4pplet/BlueSaab/CDCStatus.cpp

/* C++ class for emulating CD changer communications on SAAB I-bus
 * Copyright (C) 2018 Girts Linde
 *
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
 * You should have received a copy of the GNU General Public License
 * along with this program.  If not, see <https://www.gnu.org/licenses/>.
 */

#include <string.h>
#include "CDCStatus.h"
#include "IbusProtocol.h"
#include "SaabCan.h"
#include "Bluetooth.h"
#include "SidResource.h"

CDCStatus cdcStatus;

// The 0x6A2 node-status reply sequences live in IbusProtocol (frozen,
// host-tested against docs/IBUS_PROTOCOL.md).

unsigned char soundCmd[] = {0x80,0x04,0x00,0x00,0x00,0x00,0x00,0x00};

/*
 * All three node-status reply sequences share frame ID 0x6A2, so they must
 * go through ONE thread: with a sender thread per sequence (as before
 * v6.1.4), two IHU state flips in quick succession could interleave two
 * sequences on the bus - violating the >=10 ms same-ID spacing rule and
 * scrambling the reply order the 9-5 IHU is strict about.
 */
class NodeStatusSender {
	Thread thread;
	uint32_t lastFrameSent;
	bool sentAnything;

	void sendSequence(const unsigned char frames[][8]) {
		// Seam guard: >=10 ms between same-ID frames also across sequence
		// boundaries (a poll arriving mid-sequence would otherwise start
		// the next sequence back-to-back with the previous one's last frame).
		if (sentAnything) {
			uint32_t since_ms = (us_ticker_read() - lastFrameSent) / 1000;
			if (since_ms < 10)
				Thread::wait(10 - since_ms);
		}
		for (int i = 0; i < ibus::NODE_STATUS_FRAMES; i++) {
			if (i > 0)
				Thread::wait(NODE_STATUS_TX_INTERVAL);
			saabCan.sendCanFrame(NODE_STATUS_TX_CDC, frames[i]);
		}
		lastFrameSent = us_ticker_read();
		sentAnything = true;
	}

	void run() {
		while (1) {
			osEvent evt = Thread::signal_wait(0); // wait for any request flag
			if (evt.status != osEventSignal)
				continue;
			int32_t sig = evt.value.signals;
			// signal_wait returns and clears ALL pending flags - answer every
			// requested sequence rather than dropping the lower-priority ones
			// (the 9-5 IHU requires each poll to be answered).
			if (sig & 0x8)
				sendSequence(ibus::nodeStatusFrames(ibus::NODE_REPLY_POWER_DOWN));
			if (sig & 0x1)
				sendSequence(ibus::nodeStatusFrames(ibus::NODE_REPLY_ACTIVE));
			if (sig & 0x4)
				sendSequence(ibus::nodeStatusFrames(ibus::NODE_REPLY_POWER_ON));
		}
	}

public:
	NodeStatusSender(): thread(osPriorityNormal, 320), lastFrameSent(0), sentAnything(false) {
		thread.start(callback(this, &NodeStatusSender::run));
		#if STACK_MONITOR_ENABLED
			getLog()->registerThread("NodeStatusSender::run", &thread);
		#endif
	}
	void send(int32_t signal) {
		thread.signal_set(signal);
	}
};

NodeStatusSender nodeStatusSender;

void CDCStatus::initialize() {
	saabCan.attach(NODE_STATUS_RX_IHU, callback(this, &CDCStatus::onIhuStatusFrame));
	saabCan.attach(CDC_CONTROL, callback(this, &CDCStatus::onCDCControlFrame));
//	getLog()->log("CDCStatus::initialize()\r\n");
	thread.start(callback(this, &CDCStatus::run));
	#if STACK_MONITOR_ENABLED
		getLog()->registerThread("CDCStatus::run", &thread);
	#endif
}

void CDCStatus::onCDCControlFrame(CANMessage& frame) {
	switch (ibus::decodeCdcCommand(frame.data)) {
		case ibus::CDC_CMD_ON:
			cdcActive = true;
			#if SID_TEXT_CONTROL_ENABLED
				{
					// Show firmware + RN52 versions for a few seconds, e.g.
					// "6.1.7 R1.16". Built by hand - this runs in the CAN RX
					// interrupt, where printf-family calls are not safe.
					char verText[13];
					// compile-time check: prefix + NUL must leave room in verText
					typedef char verTextFits[(sizeof(FIRMWARE_VERSION " R") < sizeof(verText)) ? 1 : -1];
					(void)sizeof(verTextFits);
					strcpy(verText, FIRMWARE_VERSION " R");
					strncat(verText, bluetooth.getRN52Version(),
							sizeof(verText) - sizeof(FIRMWARE_VERSION " R"));
					sidResource.showTemporary(verText, 4);
				}
				sidResource.activate();
			#endif
			#if CDC_ENTRY_BEEP_ENABLED
				saabCan.sendCanFrame(SOUND_REQUEST, soundCmd);
			#endif
			thread.signal_set(0x2);
			bluetooth.connectable();
			bluetooth.reconnect();
			break;
		case ibus::CDC_CMD_OFF:
			#if SID_TEXT_CONTROL_ENABLED
				sidResource.deactivate();
			#endif
			cdcActive = false;
			thread.signal_set(0x2);
			bluetooth.disconnect();
			break;
		case ibus::CDC_CMD_NONE:
			break;
	}
}

void CDCStatus::onIhuStatusFrame(CANMessage& frame) {

	// "Here be dragons": the poll's byte 3 selects the reply (IbusProtocol).
	switch (ibus::nodeReplyFor(frame.data)) {
	case ibus::NODE_REPLY_POWER_ON:
		nodeStatusSender.send(0x4);
		break;
	case ibus::NODE_REPLY_ACTIVE:
		nodeStatusSender.send(0x1);
		break;
	case ibus::NODE_REPLY_POWER_DOWN:
		nodeStatusSender.send(0x8);
		break;
	case ibus::NODE_REPLY_NONE:
		break;
	}
}

void CDCStatus::run() {
//	getLog()->log("CDCStatus::run()\r\n");
	bool cdcStatusResendNeeded = false;
	bool cdcStatusResendDueToCdcCommand = false;

	while(1) {
//		getLog()->log("cdcActive %d\r\n", cdcActive);
		sendCdcStatus(cdcStatusResendNeeded, cdcStatusResendDueToCdcCommand, cdcActive);
		Thread::wait(50);
		cdcStatusResendNeeded = false;
		cdcStatusResendDueToCdcCommand = false;
		osEvent result = Thread::signal_wait(0x2, CDC_STATUS_TX_BASETIME-50);
		if (result.status == osEventSignal) {
			cdcStatusResendNeeded = true;
			cdcStatusResendDueToCdcCommand = true;
		}
	}
}

void CDCStatus::sendCdcStatus(bool event, bool remote, bool cdcActive) {
	// Frame layout documented in IbusProtocol.cpp / docs/IBUS_PROTOCOL.md
	unsigned char cdcGeneralStatusCmd[8];
	ibus::buildCdcStatus(cdcGeneralStatusCmd, event, remote, cdcActive);
	saabCan.sendCanFrame(GENERAL_STATUS_CDC, cdcGeneralStatusCmd);
}
