4pplet/BlueSaab/SaabCan.h

/* C++ class for handling/emulating node communications on SAAB I-bus
 * Copyright (C) 2018 Girts Linde
 *
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
 * You should have received a copy of the GNU General Public License
 * along with this program.  If not, see <https://www.gnu.org/licenses/>.
 */

#ifndef SAABCAN_H_
#define SAABCAN_H_

#include "rtos.h"
#include "SerialLog.h"

/**
 * TX frames:
 */

#define GENERAL_STATUS_CDC			0x3C8
#define NODE_STATUS_TX_CDC			0x6A2
#define SOUND_REQUEST				0x430

/**
 * RX frames:
 */

#define CDC_CONTROL					0x3C0
#define DISPLAY_RESOURCE_GRANT		0x368
#define NODE_STATUS_RX_IHU			0x6A1
#define STEERING_WHEEL_BUTTONS		0x290
#define IHU_DISPLAY_RESOURCE_REQ	0x348

/**
 * Time interval definitions:
 */

#define NODE_STATUS_TX_INTERVAL		140 			// Replies to '6A1' request need to be sent with no more than 140ms interval; tolerances +/- 10%
#define CDC_STATUS_TX_BASETIME		950 			// The CDC status frame must be sent periodically within this time-frame; tolerances +/- 10%
#define NODE_UPDATE_BASETIME		1000

/**
 * Other useful stuff
 */

#define MODULE_NAME					"BlueSaab v6"
#define FIRMWARE_VERSION			"6.1.7"

// Set to 0 to suppress the SID beep on entering CDC mode (recommended for
// 9-5s if chasing warning-light issues - see docs/SAAB_9-5_NOTES.md)
#ifndef CDC_ENTRY_BEEP_ENABLED
#define CDC_ENTRY_BEEP_ENABLED		1
#endif
#define LAST_EVENT_IN_TIMEOUT		3000 		    // Milliseconds

struct FrameCallback {
	unsigned int id;
	Callback<void(CANMessage&)> callBack;
	FrameCallback(): id(0) {}
};

class SaabCan {
	enum {CAN_MAX_CALLBACKS = 10};
	Mail <CANMessage, 16> canFrameQueue;
	FrameCallback callBacks[CAN_MAX_CALLBACKS];
	Thread send_thread;
	volatile unsigned txErrors;
	volatile unsigned txDropped;
	enum {TX_SPACING_SLOTS = 8}; // we transmit 5 distinct IDs
	unsigned lastTxId[TX_SPACING_SLOTS];   // send-thread only; zero at boot
	uint32_t lastTxTime[TX_SPACING_SLOTS];

	void sendFunc();
	int spaceSameId(unsigned id);
public:
	// lastTxId/lastTxTime rely on static zero-init: the only instance is the
	// global saabCan. Don't create a SaabCan with automatic/dynamic storage.
	// cppcheck-suppress uninitMemberVar
	SaabCan(): send_thread(osPriorityNormal, 320), txErrors(0), txDropped(0) {}
	unsigned getTxErrors() { return txErrors; }
	unsigned getTxDropped() { return txDropped; }
	// Live bxCAN error state (read-only register reads, ISR-safe)
	unsigned getRxErrorCounter();
	unsigned getTxErrorCounter();
	uint32_t getESR();
	void initialize(int hz);
	void sendCanFrame(int canId, const unsigned char *data);
	void onRx();
	void attach(unsigned int canId, Callback<void(CANMessage&)>);
};

extern SaabCan saabCan;

#endif /* SAABCAN_H_ */
