4pplet/BlueSaab/common/SerialLog.cpp

/* C++ class for STM32F103RB microcontroller logging
 * Copyright (C) 2018 Girts Linde
 *
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
 * You should have received a copy of the GNU General Public License
 * along with this program.  If not, see <https://www.gnu.org/licenses/>.
 */

#include "SerialLog.h"

Serial pcSerial(PA_2, PA_3, 115200); // UART2

SerialLog *logInstance = NULL;

SerialLog *getLog() {
	if (logInstance == NULL) {
		logInstance = new SerialLog(pcSerial);
	}
	return logInstance;
}


void SerialLog::onSerialRx(int p) {
	if (p & SERIAL_EVENT_RX_COMPLETE) {
		if (rxCallback) {
			rxCallback.call(rxChar);
		}
	}

	serial.read((uint8_t*)&rxChar, 1, callback(this, &SerialLog::onSerialRx), SERIAL_EVENT_RX_COMPLETE);
}

void SerialLog::run() {
	serial.read((uint8_t*)&rxChar, 1, callback(this, &SerialLog::onSerialRx), SERIAL_EVENT_RX_COMPLETE);

	uint32_t last_threads_printed = us_ticker_read();
	while(true) {
		osEvent evt = mail_box.get(1000); // Timeout to print thread info periodically
		if (evt.status == osEventMail) {
			LogEntry *e = (LogEntry*)evt.value.p;
			serial.printf("%05d ", e->time/1000);
			switch ((int)e->format) {
				case leCANMessage: {
					CANMessage *m = (CANMessage *) e->value;
					if (m->type == CANData)
						serial.printf(
								"%#x %c %d: %02x %02x %02x %02x %02x %02x %02x %02x\r\n",
								m->id, (m->format == CANStandard) ? 's' : 'x',
								m->len, m->data[0], m->data[1], m->data[2],
								m->data[3], m->data[4], m->data[5], m->data[6],
								m->data[7]);
					else
						serial.printf("%#x %c: remote\r\n", m->id,
								(m->format == CANStandard) ? 's' : 'x');
					delete m;
					break;
				}
				case leShortString: {
					// 4 chars packed into the int value by logShortString()
					// cppcheck-suppress dangerousTypeCast
					char *p = (char*)&e->value;
					for(int i=0; i<4; i++) {
						if (*p == 0 || *p == '\r' || *p == '\n')
							break;
						serial.putc(*p);
						p++;
					}
					serial.puts("\r\n");
					break;
				}
				default: {
					serial.printf(e->format, e->value);
					size_t l = strlen(e->format);
					if (l==0 || e->format[l-1]!='\n')
						serial.putc('\n');
				}
			}
			mail_box.free(e);
		}
		uint32_t time_now = us_ticker_read();
		int time_since_print = time_now - last_threads_printed;
		if (time_since_print > 1000000) {
			last_threads_printed = time_now;
			printThreads();
		}
	}
}

void SerialLog::printThreads() {
	for(unsigned i=0; i<monitored_threads.size(); i++) {
		serial.printf("thread %20s size %4u, max used %u\r\n",
				monitored_threads[i].name,
				monitored_threads[i].thread->stack_size(),
				monitored_threads[i].thread->max_stack());
	}
}

void SerialLog::log(const char* format, int value) {
	LogEntry *e = mail_box.alloc();
	if (e == NULL)
		return; // log queue full - drop the line rather than hardfault
	e->time = us_ticker_read();
	e->format = format;
	e->value = value;
	mail_box.put(e);
}

// NOT ISR-safe (heap allocation) - call from thread context only.
void SerialLog::logFrame(CANMessage* frame) {
	LogEntry *e = mail_box.alloc();
	if (e == NULL)
		return; // check the mailbox BEFORE allocating, or the copy leaks
	CANMessage *saved_frame = new CANMessage();
	*saved_frame = *frame;
	e->time = us_ticker_read();
	e->format = (char *)leCANMessage;
	e->value = (int)saved_frame;
	mail_box.put(e);
}

void SerialLog::logShortString(const char *s) {
	uint32_t buf;
	// the int is only a 4-byte carrier for chars - see run()
	// cppcheck-suppress dangerousTypeCast
	strncpy((char *)&buf, s, 4);
	// sentinel "format" pointer (leShortString = 1) - see run()
	log((char *)leShortString, buf);
}
