4pplet/BlueSaab/SaabCan.cpp

/* C++ class for handling/emulating node communications on SAAB I-bus
 * Copyright (C) 2018 Girts Linde
 *
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
 * You should have received a copy of the GNU General Public License
 * along with this program.  If not, see <https://www.gnu.org/licenses/>.
 */

#include "mbed.h"
#include "rtos.h"
#include "SaabCan.h"

extern "C" void can_reset_rx_overruns(void);

// Construct at the real I-Bus bitrate: the default CAN() ctor would join
// the live car bus at 100 kbit/s error-active during static init, actively
// corrupting frames every ignition-on until initialize() fixed the rate.
CAN iBus(PB_8, PB_9, 47619);
CANMessage canRxFrame;
SaabCan saabCan;

void SaabCan::initialize(int hz) {
	// The constructor already set the bitrate; re-applying it here is the
	// second chance if that failed. Normal mode only once the bitrate is
	// right: after a failed setup the controller may still hold the HAL's
	// placeholder 1.2 Mbit/s timing in silent mode, and leaving silent mode
	// there would put an error-active node at the wrong bitrate on the car's
	// bus (6.1.1 gated this the same way). Neither step may halt the unit.
	if (iBus.frequency(hz)) {
		if (!iBus.mode(CAN::Normal))
			getLog()->log("CAN: normal mode setup failed\r\n");
	} else {
		getLog()->log("CAN: bitrate setup failed\r\n");
	}

	iBus.attach(callback(this,&SaabCan::onRx), mbed::CAN::RxIrq);
	// The controller has been receiving since static init, before this
	// handler existed: overruns of its 3-deep FIFO until now don't count.
	can_reset_rx_overruns();
	send_thread.start(callback(this, &SaabCan::sendFunc));
	#if STACK_MONITOR_ENABLED
		getLog()->registerThread("SaabCan::sendFunc", &send_thread);
	#endif
}

void SaabCan::sendCanFrame(int canId, const unsigned char *data) {
	CANMessage *box = canFrameQueue.alloc();
	if (box == NULL) {
		txDropped++;
		return; // TX queue full - drop the frame rather than hardfault
	}
	CANMessage *canTxFrame = new (box) CANMessage();
	canTxFrame->id = canId;
	for (int i = 0; i < canTxFrame->len; i++) {
		canTxFrame->data[i] = data[i];
	}
	canFrameQueue.put(canTxFrame);
}

extern DigitalOut aliveLed;

void SaabCan::onRx() {
	while (iBus.read(canRxFrame)) {
		// The I-Bus carries 11-bit data frames only. Anything else could
		// alias a handled ID (a remote frame would replay stale data[]).
		if (canRxFrame.format != CANStandard || canRxFrame.type != CANData)
			continue;
		for (int i = 0; i < CAN_MAX_CALLBACKS; i++) {
			// Unused slots have id 0 and an empty callback: calling one is
			// an MBED_ASSERT -> permanent halt, so an ID-0 frame on the bus
			// used to kill the unit.
			if (callBacks[i].id != 0 && callBacks[i].id == canRxFrame.id
					&& callBacks[i].callBack) {
				callBacks[i].callBack.call(canRxFrame);
			}
		}
	}
}

void SaabCan::sendFunc() {
	while (true) {
		osEvent evt = canFrameQueue.get();
		if (evt.status == osEventMail) {
			CANMessage *message = (CANMessage*) evt.value.p;
//			getLog()->logFrame(message);
//			unsigned tde = iBus.tderror();

			int slot = spaceSameId(message->id);

			// All 3 TX mailboxes busy (lost arbitration under load): retry for
			// up to ~20 ms instead of dropping at once - a lost 0x6A2 breaks
			// the 9-5 handshake, a lost 0x337 tears SID text. Single consumer,
			// so frame order is kept.
			int tries = 0;
			bool sent = true;
			while (iBus.write(*message) == 0) {
				if (++tries > 20) {
					txErrors++; // dropped
					sent = false;
					break;
				}
				Thread::wait(1);
			}
			if (sent) {
				lastTxId[slot] = message->id;
				lastTxTime[slot] = us_ticker_read();
			}
//			unsigned rde = iBus.rderror();
//			tde = iBus.tderror();
//			getLog()->log("    rde=%d\r\n", rde);
//			getLog()->log("    tde=%d\r\n", tde);
//
//			uint32_t esr = iBus.read_ESR();
//			getLog()->log("    ESR=%08x\r\n", esr);
//			getLog()->log("    BOFF=%x\r\n", esr & 4);
//			getLog()->log("    MCR=%08x\r\n", iBus.read_MCR());

			canFrameQueue.free(message);
			aliveLed = !aliveLed;
		}
	}
}

unsigned SaabCan::getRxErrorCounter() {
	return iBus.rderror();
}

unsigned SaabCan::getTxErrorCounter() {
	return iBus.tderror();
}

uint32_t SaabCan::getESR() {
	return iBus.read_ESR();
}

// Same-ID frames should be >=10 ms apart on the bus. Producers already space
// their groups, but a retry delay in sendFunc can bunch the next frame of a
// group up behind the delayed one, so enforce the spacing here too (measured
// when the frame is handed to a mailbox). RTX waits end on a 1 ms tick, so
// the guaranteed minimum is ~9 ms (typically 10-11 ms) - the same margin the
// field-proven MessageSender 10 ms interval always had. Returns the slot to
// record into.
int SaabCan::spaceSameId(unsigned id) {
	int freeSlot = -1;
	for (int i = 0; i < TX_SPACING_SLOTS; i++) {
		if (lastTxId[i] == id) {
			uint32_t since_us = us_ticker_read() - lastTxTime[i];
			if (since_us < 10000)
				Thread::wait((10000 - since_us) / 1000 + 1);
			return i;
		}
		if (lastTxId[i] == 0 && freeSlot < 0)
			freeSlot = i;
	}
	return freeSlot >= 0 ? freeSlot : 0; // more IDs than slots: reuse slot 0
}

void SaabCan::attach(unsigned int canId, Callback<void(CANMessage&)> callBack) {
	for (int i = 0; i < CAN_MAX_CALLBACKS; i++) {
		if (callBacks[i].id == 0) {
			callBacks[i].callBack = callBack;
			callBacks[i].id = canId;
			return;
		}
	}
	getLog()->log("SaabCan::attach: table full, callback for id %x DROPPED\r\n", canId);
}
