4pplet/BlueSaab/Buttons.cpp

/* C++ class for SAAB infotainment head unit and steering wheel button event handling
 * Copyright (C) 2018 Girts Linde
 *
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
 * You should have received a copy of the GNU General Public License
 * along with this program.  If not, see <https://www.gnu.org/licenses/>.
 */

#include "Buttons.h"
#include "IbusProtocol.h"
#include "Bluetooth.h"
#include "SidResource.h"

Buttons buttons;

Buttons::Buttons() {
}

void Buttons::initialize() {
	saabCan.attach(CDC_CONTROL, callback(this, &Buttons::onFrame));
}

void Buttons::onFrame(CANMessage& frame) {
	ibus::Button button = ibus::decodeButton(frame.data);
	if (button != ibus::NONE) {
#if SID_TEXT_CONTROL_ENABLED
		// Driver breakthrough only for actual (recognized) button presses -
		// not for every 0x80-flagged frame (mode changes, pause, unmapped
		// codes), which needlessly escalated our display requests.
		sidResource.requestDriverBreakthrough();
#endif
//		getLog()->log("Buttons::onFrame button %d", button);
		switch (ibus::buttonAction(button)) {
		case ibus::ACT_PLAY_PAUSE:
			bluetooth.play();
			break;
		case ibus::ACT_NEXT:
			bluetooth.next();
			break;
		case ibus::ACT_PREV:
			bluetooth.prev();
			break;
		case ibus::ACT_PAIR:
			bluetooth.discoverable();
			#if SID_TEXT_CONTROL_ENABLED
				sidResource.showTemporary("PAIRING", 10); // ~10 s, like STP,10 (actual discoverable window undocumented)
			#endif
			break;
		case ibus::ACT_RECONNECT:
			bluetooth.reconnect();
			break;
		case ibus::ACT_VOLUME_DOWN:
			bluetooth.volumeDown();
			break;
		case ibus::ACT_VOLUME_UP:
			bluetooth.volumeUp();
			break;
		case ibus::ACT_DISCONNECT:
			bluetooth.disconnect();
			break;
		case ibus::ACT_NONE:
			break;
		}
	} else {
//		getLog()->log("Buttons::onFrame button unknown");
	}
}
