4pplet/BlueSaab/SidResource.h

/* C++ class for handling SID (SAAB Information Display) resource requests and write access
 * Copyright (C) 2018 Girts Linde
 *
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
 * You should have received a copy of the GNU General Public License
 * along with this program.  If not, see <https://www.gnu.org/licenses/>.
 */

#ifndef SAAB_CDC_SIDRESOURCE_H_
#define SAAB_CDC_SIDRESOURCE_H_
#ifndef SID_TEXT_CONTROL_ENABLED
#define SID_TEXT_CONTROL_ENABLED			1
#endif

#include <rtos.h>
#include "MessageSender.h"
#include "Scroller.h"


class SidResource {
	unsigned char sidMessageGroup[3][8];
	MessageSender textSender;

	volatile bool sidDriverBreakthroughNeeded;
	volatile bool sidWriteAccessWanted;

	char tempText[13];
	volatile int tempGrants;
	uint32_t lastTextSend;

	volatile bool writeTextOnDisplayUpdateNeeded; // set in the CAN ISR (activate)

	Thread thread;

	void run();

	void sendDisplayRequest(bool driverBreakthrough);
	void handleSignals(int32_t signals);
	void writeGrantedText();
	void formatTextMessage(const char textIn[], bool event);
public:
	SidResource();
	~SidResource();

	void initialize();
	// Show a fixed text (max 12 chars) for the next 'grants' display grants
	// (roughly one grant per second) instead of the scroller content.
	void showTemporary(const char *text, int grants);
	void requestDriverBreakthrough() {
		sidDriverBreakthroughNeeded = true;
		thread.signal_set(0x10);
	}
	// activate()/deactivate() are called from the CAN RX ISR. The scroller
	// clear must NOT happen here: the scroller's semaphore cannot be taken
	// in an ISR (RTX refuses and returns an error - unchecked, it silently
	// skips locking) but release DOES work in an ISR, so an ISR-side
	// wait/release pair inflates the semaphore by one token each time,
	// permanently breaking the lock. The thread does the clear instead
	// (signal 0x40).
	void activate() {
		sidWriteAccessWanted = true;
		writeTextOnDisplayUpdateNeeded = true;
		thread.signal_set(0x40);
	}
	void deactivate() {
		sidWriteAccessWanted = false;
		thread.signal_set(0x40);
	}

	void grantReceived(CANMessage& frame);
	void ihuRequestReceived(CANMessage& frame);
};

	#if SID_TEXT_CONTROL_ENABLED
		extern SidResource sidResource;
	#endif

#endif /* SAAB_CDC_SIDRESOURCE_H_ */
